CPSCourse-TUM-HN/connecTUM/kicad_schematics/Adafruit PCA9685 rev C.kicad_sch

## KiCad design kicad_schematics/Adafruit PCA9685 rev C.kicad_sch (2025-07-12)

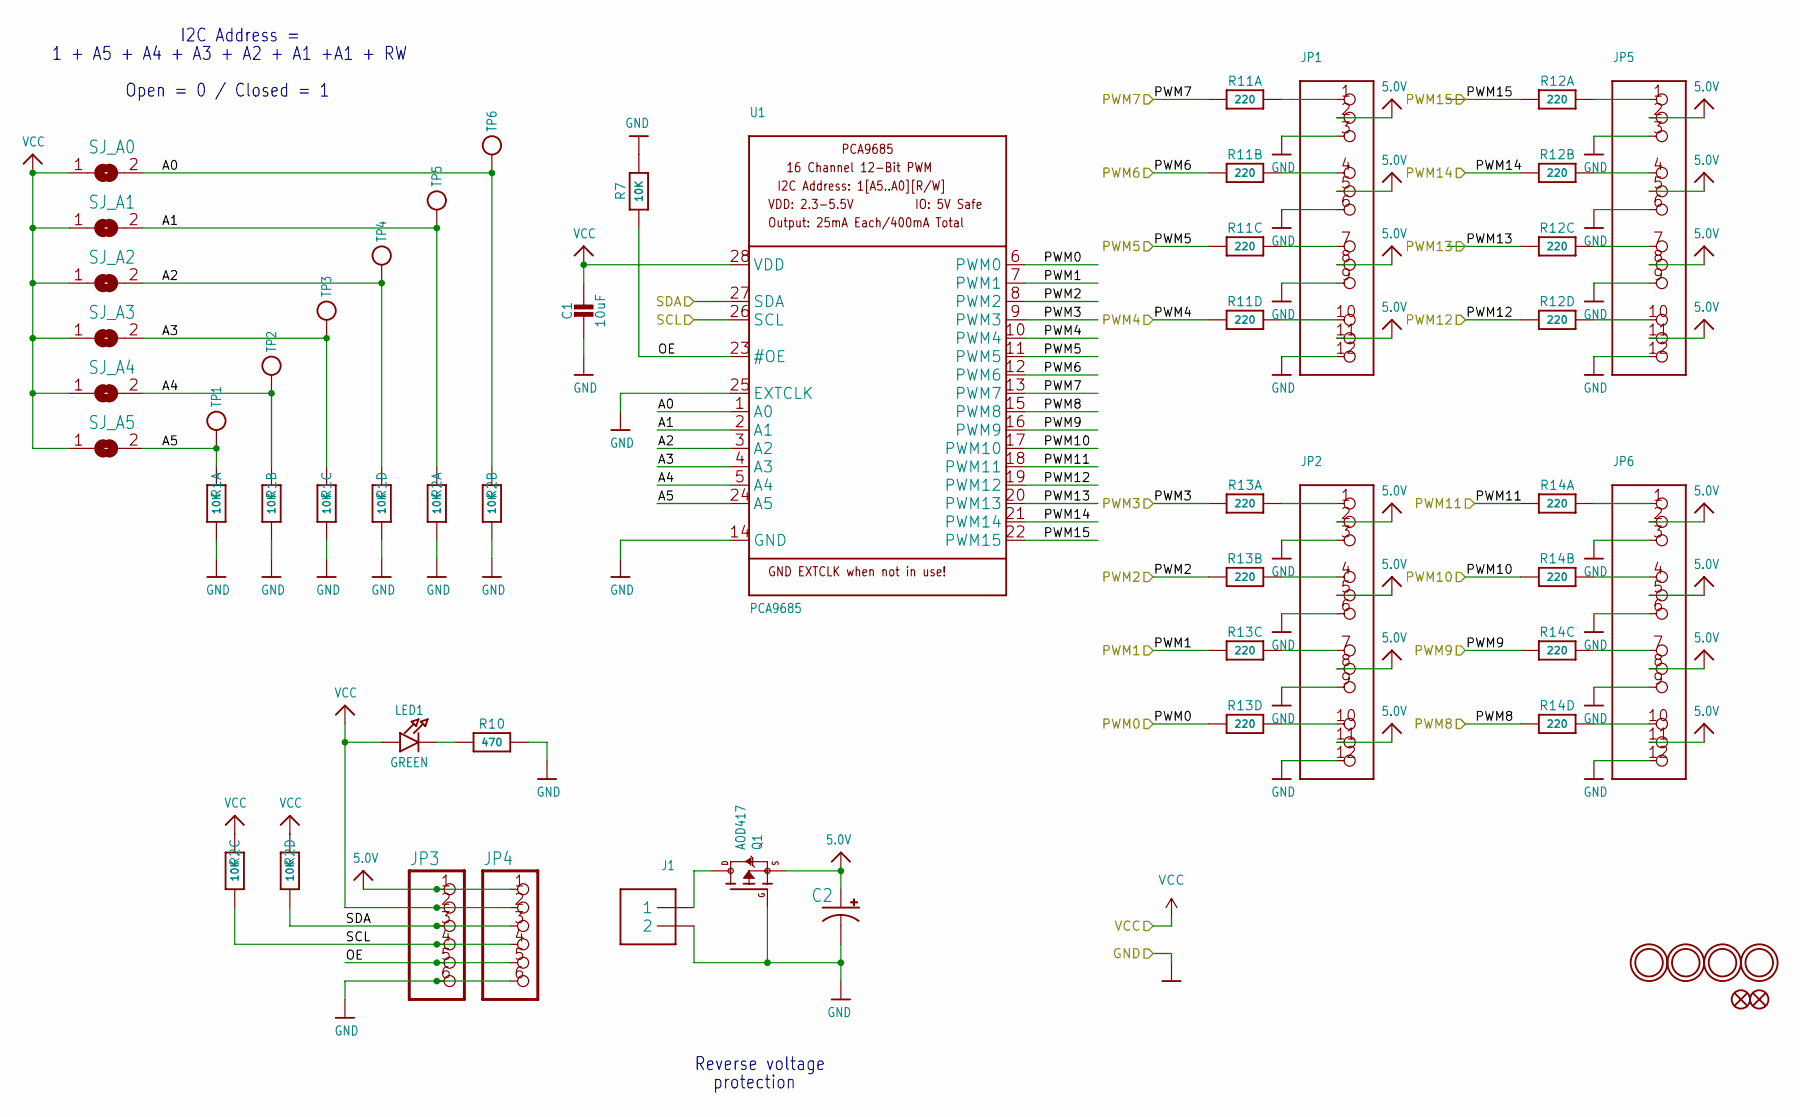
[picture p21: schematic Adafruit PCA9685 rev C.kicad_sch]

Parts:
01: (no value)
C1: 10uF; 0805-NO
C2: CPOL-USE3.5-8; E3,5-8
FID1, FID2: FIDUCIAL""; FIDUCIAL_1MM
J1: TERMBLOCK_1X2; TERMBLOCK_1X2-3.5MM
JP1, JP2, JP5, JP6: HEADER-3X04; 3X04
JP3, JP4: PINHD-1X6CB; 1X06-CLEANBIG
LED1: GREEN; CHIPLED_0805_NOOUTLINE
Q1: AOD417; TO252
R1, R2: 10K; RESPACK_4X0603
R7: 10K; 0805-NO
R10: 470; _0805MP
R11, R12, R13, R14: 220; RESPACK_4X0603
SJ_A0, SJ_A1, SJ_A2, SJ_A3, SJ_A4, SJ_A5: SOLDERJUMPERREFLOW_NOPASTE; SOLDERJUMPER_REFLOW_NOPASTE
TP1, TP2, TP3, TP4, TP5, TP6: TESTPOINTROUND1MM; TESTPOINT_ROUND_1MM
U1: PCA9685; TSSOP28
U$47, U$48, U$49, U$50: MOUNTINGHOLE2.5; MOUNTINGHOLE_2.5_PLATED

Connections:
5.0V: C2.+, JP1.2, JP1.5, JP1.8, JP1.11, JP2.2, JP2.5, JP2.8, JP2.11, JP3.1, JP4.1, JP5.2, JP5.5, JP5.8, JP5.11, JP6.2, JP6.5, JP6.8, JP6.11, Q1.2 (S)
A0: R2.7 (2), SJ_A0.2, TP6.P$1, U1.1 (A0)
A1: R2.8 (2), SJ_A1.2, TP5.P$1, U1.2 (A1)
A2: R1.5 (2), SJ_A2.2, TP4.P$1, U1.3 (A2)
A3: R1.6 (2), SJ_A3.2, TP3.P$1, U1.4 (A3)
A4: R1.7 (2), SJ_A4.2, TP2.P$1, U1.5 (A4)
A5: R1.8 (2), SJ_A5.2, TP1.P$1, U1.24 (A5)
GND: 01.1, C1.2, C2.-, J1.2, JP1.3, JP1.6, JP1.9, JP1.12, JP2.3, JP2.6, JP2.9, JP2.12, JP3.6, JP4.6, JP5.3, JP5.6, JP5.9, JP5.12, JP6.3, JP6.6, JP6.9, JP6.12, Q1.1 (G), R1.1, R1.2 (1), R1.3 (1), R1.4 (1), R2.1, R2.2 (1), R7.2, R10.2, U1.14 (GND), U1.25 (EXTCLK)
unnamed: J1.1, Q1.3 (D)
unnamed: JP1.1, R11.8 (2)
unnamed: JP1.4, R11.7 (2)
unnamed: JP1.7, R11.6 (2)
unnamed: JP1.10, R11.5 (2)
unnamed: JP2.1, R13.8 (2)
unnamed: JP2.4, R13.7 (2)
unnamed: JP2.7, R13.6 (2)
unnamed: JP2.10, R13.5 (2)
unnamed: JP5.1, R12.8 (2)
unnamed: JP5.4, R12.7 (2)
unnamed: JP5.7, R12.6 (2)
unnamed: JP5.10, R12.5 (2)
unnamed: JP6.1, R14.8 (2)
unnamed: JP6.4, R14.7 (2)
unnamed: JP6.7, R14.6 (2)
unnamed: JP6.10, R14.5 (2)
unnamed: LED1.C, R10.1
OE: JP3.5, JP4.5, R7.1, U1.23 (#OE)
PWM0: R13.4 (1), U1.6 (PWM0)
PWM1: R13.3 (1), U1.7 (PWM1)
PWM2: R13.2 (1), U1.8 (PWM2)
PWM3: R13.1, U1.9 (PWM3)
PWM4: R11.4 (1), U1.10 (PWM4)
PWM5: R11.3 (1), U1.11 (PWM5)
PWM6: R11.2 (1), U1.12 (PWM6)
PWM7: R11.1, U1.13 (PWM7)
PWM8: R14.4 (1), U1.15 (PWM8)
PWM9: R14.3 (1), U1.16 (PWM9)
PWM10: R14.2 (1), U1.17 (PWM10)
PWM11: R14.1, U1.18 (PWM11)
PWM12: R12.4 (1), U1.19 (PWM12)
PWM13: R12.3 (1), U1.20 (PWM13)
PWM14: R12.2 (1), U1.21 (PWM14)
PWM15: R12.1, U1.22 (PWM15)
SCL: JP3.4, JP4.4, R2.3 (1), U1.26 (SCL)
SDA: JP3.3, JP4.3, R2.4 (1), U1.27 (SDA)
VCC: C1.1, JP3.2, JP4.2, LED1.A, R2.5 (2), R2.6 (2), SJ_A0.1, SJ_A1.1, SJ_A2.1, SJ_A3.1, SJ_A4.1, SJ_A5.1, U1.28 (VDD)

Notes on the sheet:
1 + A5 + A4 + A3 + A2 + A1 +A1 + RW
Open = 0 / Closed = 1
Reverse voltage
I2C Address =
protection
