CPSCourse-TUM-HN/connecTUM/kicad_schematics/Adafruit TMC2209 Stepper Motor Driver.kicad_sch

## KiCad design kicad_schematics/Adafruit TMC2209 Stepper Motor Driver.kicad_sch (2025-07-12)

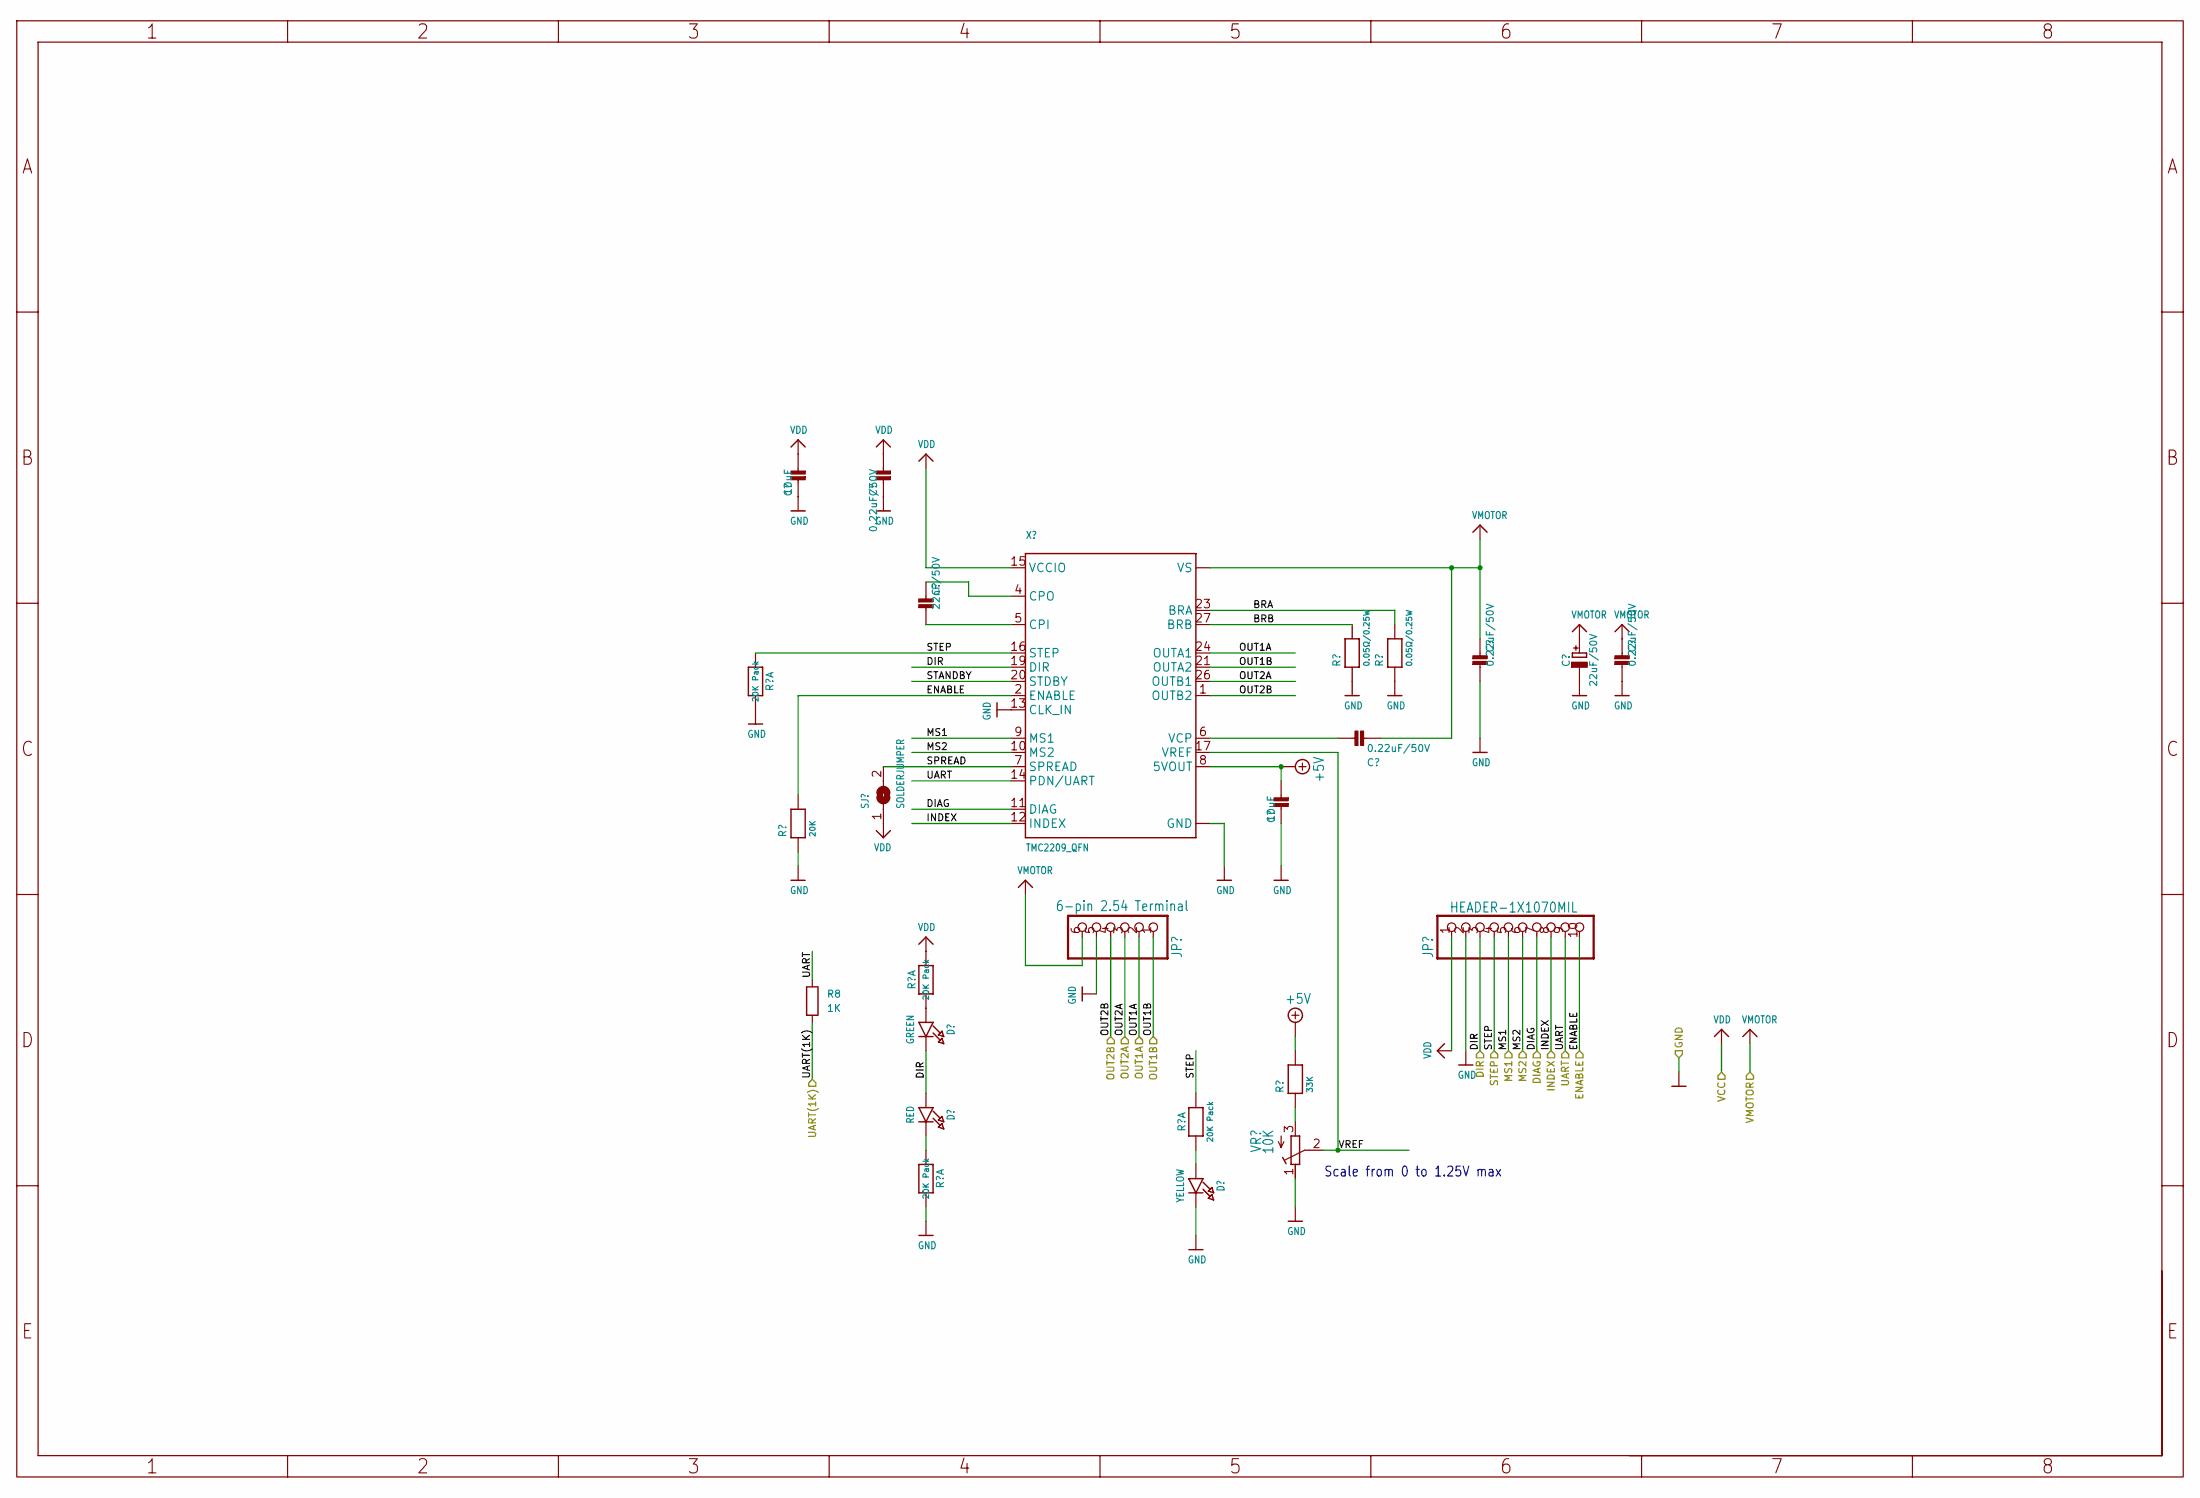
[picture p22: schematic Adafruit TMC2209 Stepper Motor Driver.kicad_sch]

Parts:
01: (no value)
C1: 22nF/50V; 0603-NO
C2, C6: 10uF; 0805-NO
C3, C5, C7, C8: 0.22uF/50V; 0603-NO
C4: 22uF/50V; PANASONIC_C
D1: RED; CHIPLED_0603_NOOUTLINE
D2: YELLOW; CHIPLED_0603_NOOUTLINE
D3: GREEN; CHIPLED_0603_NOOUTLINE
JP1: 6-pin 2.54 Terminal; 1X06_2.54MMTERMINAL
JP4: HEADER-1X1070MIL; 1X10_ROUND70
R1, R2: 0.05Ω/0.25W; 0603-NO
R3: 20K; 0603-NO
R4: 33K; 0603-NO
R5: 20K Pack; RESPACK_4X0603
R8: 1K
SJ1: SOLDERJUMPER; SOLDERJUMPER_ARROW_NOPASTE
VR1: 10K; RTRIM3314J
X1: TMC2209_QFN; QFN28_5MM_MICROCHIP

Connections:
+5V: C6.2, R4.2, X1.8 (5VOUT)
BRA: R2.2, X1.23 (BRA)
BRB: R1.2, X1.27 (BRB)
DIAG: JP4.7, X1.11 (DIAG)
DIR: D1.A, D3.C, JP4.3, X1.19 (DIR)
ENABLE: JP4.10, R3.2, X1.2 (ENABLE)
GND: 01.1, C2.1, C3.1, C4.-, C5.2, C6.1, C8.2, D2.C, JP1.5, JP4.2, R1.1, R2.1, R3.1, R5.8 (2), VR1.1 (E), X1.3 (GND), X1.13 (CLK_IN), X1.18 (GND), X1.25 (GND), X1.THERMAL (GND)
INDEX: JP4.8, X1.12 (INDEX)
MS1: JP4.5, X1.9 (MS1)
MS2: JP4.6, X1.10 (MS2)
unnamed: C1.1, X1.4 (CPO)
unnamed: C1.2, X1.5 (CPI)
unnamed: C7.1, X1.6 (VCP)
unnamed: D1.C, R5.1
unnamed: D2.A, R5.1
unnamed: D3.A, R5.1
unnamed: R4.1, VR1.3 (A)
OUT1A: JP1.2, X1.24 (OUTA1)
OUT1B: JP1.1, X1.21 (OUTA2)
OUT2A: JP1.3, X1.26 (OUTB1)
OUT2B: JP1.4, X1.1 (OUTB2)
SPREAD: SJ1.2, X1.7 (SPREAD)
STANDBY: X1.20 (STDBY)
STEP: JP4.4, R5.1, R5.8 (2), X1.16 (STEP)
UART: JP4.9, R8.1, X1.14 (PDN/UART)
UART(1K): R8.2
VDD: C2.2, C3.2, JP4.1, R5.8 (2), SJ1.1, X1.15 (VCCIO)
VMOTOR: C4.+, C5.1, C7.2, C8.1, JP1.6, X1.22 (VS), X1.28 (VS)
VREF: VR1.2 (S), X1.17 (VREF)

Notes on the sheet:
Scale from 0 to 1.25V max
