CPSCourse-TUM-HN/connecTUM/kicad_schematics/connecTUM.kicad_sch

## KiCad design kicad_schematics/connecTUM.kicad_sch (2025-07-12)

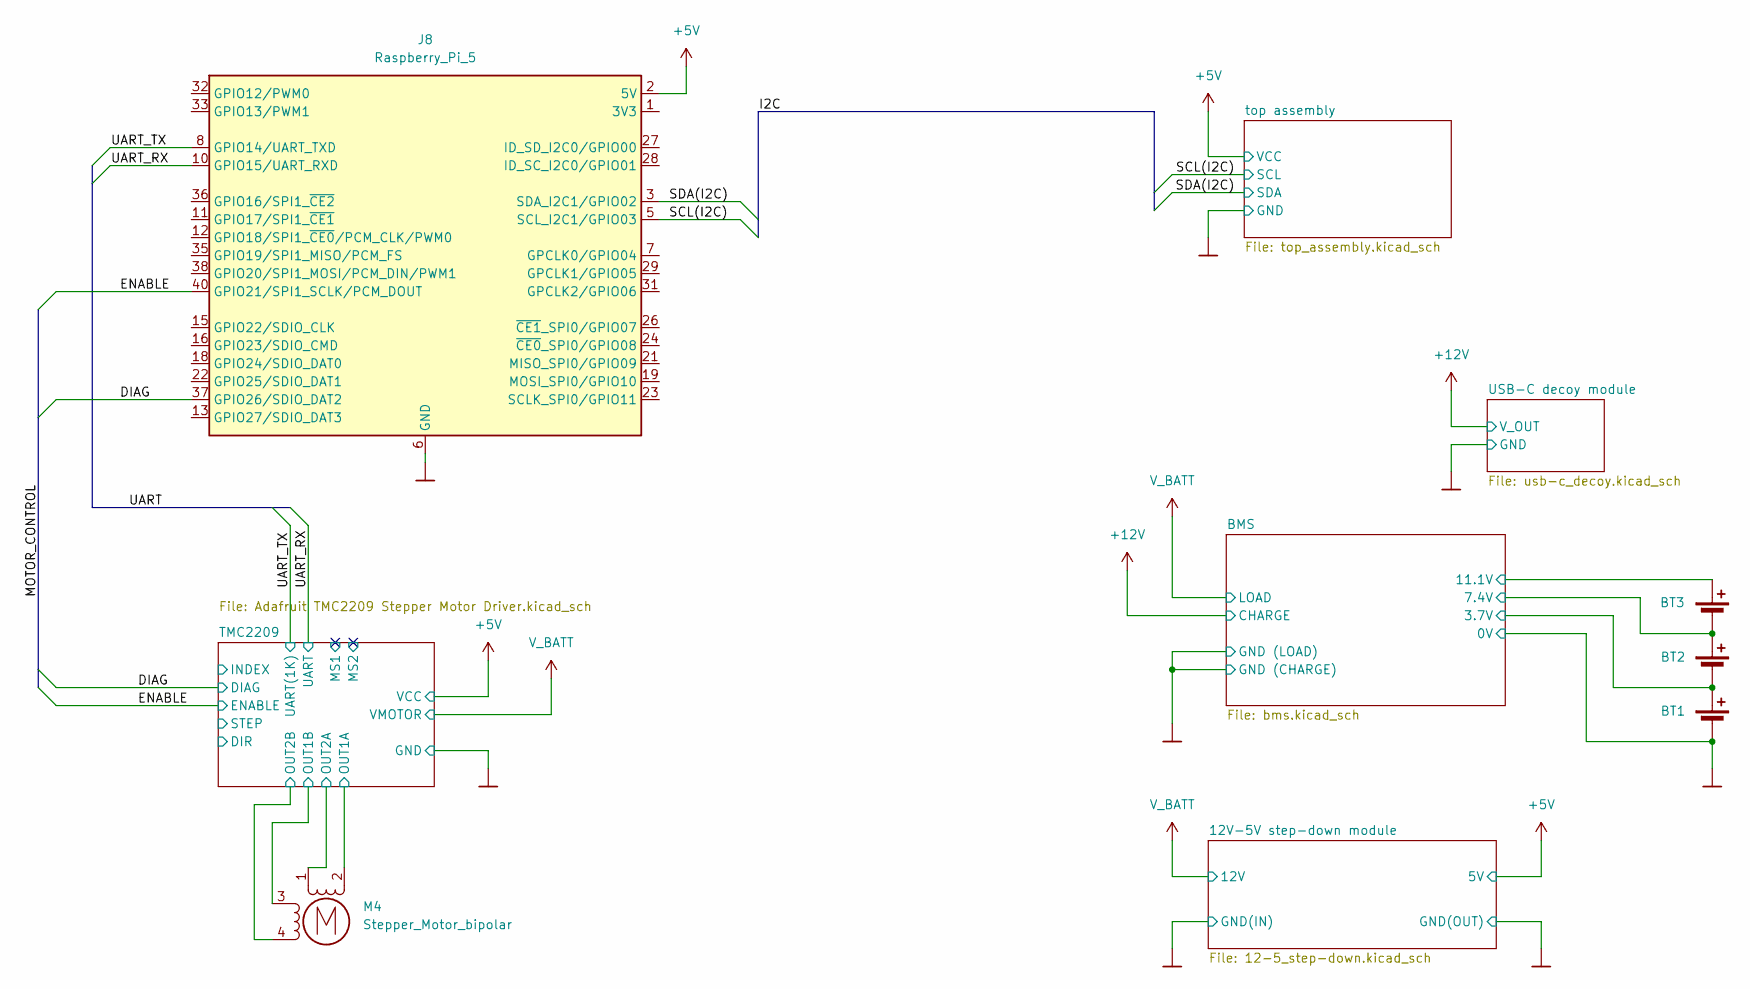
[picture p23: schematic connecTUM.kicad_sch]

Parts:
01, 0101: (no value)
BT1, BT2, BT3: Battery_Cell
J8: Raspberry_Pi_5
M4: Stepper_Motor_bipolar

Connections:
0V: 01.1, BT1.2 (-)
3.7V: BT1.1 (+), BT2.2 (-)
7.4V: BT2.1 (+), BT3.2 (-)
11.1V: BT3.1 (+)
+5V: J8.2 (5V), J8.4 (5V)
DIAG: J8.37 (GPIO26/SDIO_DAT2)
ENABLE: J8.40 (GPIO21/SPI1_SCLK/PCM_DOUT)
GND: 01.1
GND (CHARGE): 0101.1
GND(IN): 01.1
GND(OUT): 01.1
unnamed: 01.1, J8.6 (GND), J8.9 (GND), J8.14 (GND), J8.20 (GND), J8.25 (GND), J8.30 (GND), J8.34 (GND), J8.39 (GND)
unnamed: J8.1 (3V3), J8.17 (3V3)
OUT1A: M4.2 (-)
OUT1B: M4.3
OUT2A: M4.1
OUT2B: M4.4
SCL(I2C): J8.5 (SCL_I2C1/GPIO03)
SDA(I2C): J8.3 (SDA_I2C1/GPIO02)
UART_RX: J8.10 (GPIO15/UART_RXD)
UART_TX: J8.8 (GPIO14/UART_TXD)
