CPSCourse-TUM-HN/connecTUM/kicad_schematics/pcf8574.kicad_sch

## KiCad design kicad_schematics/pcf8574.kicad_sch (2025-07-12)

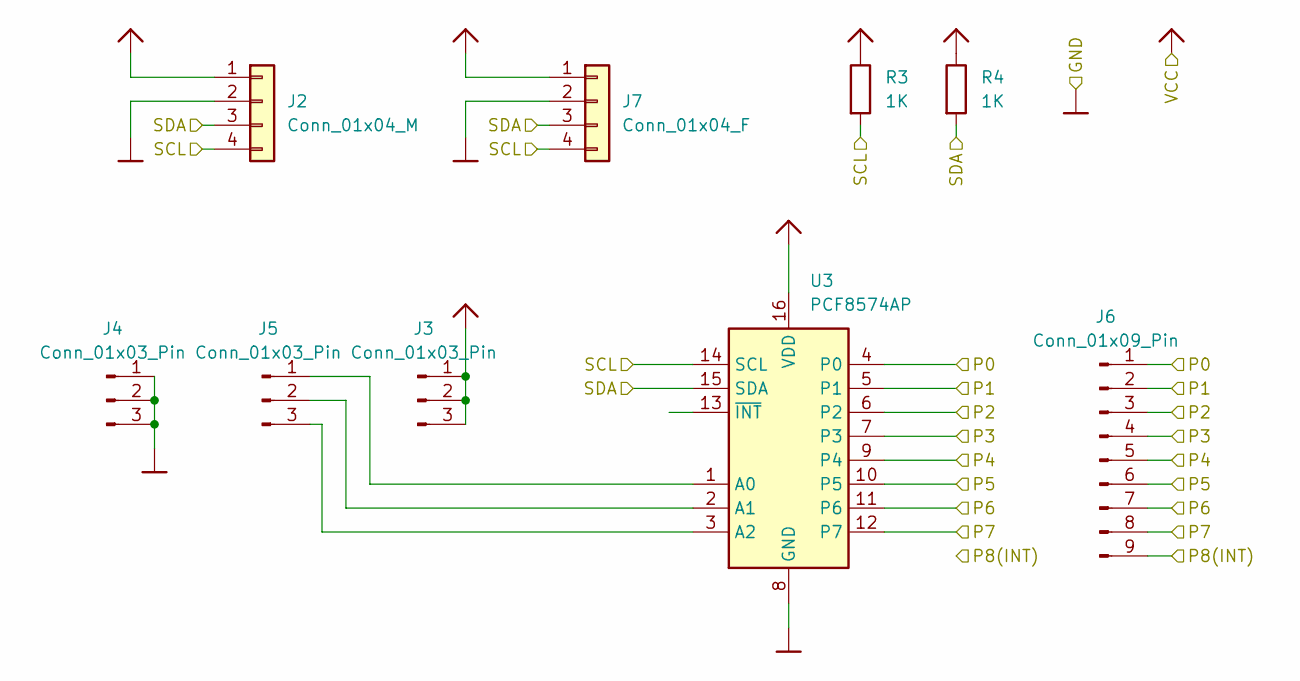
[picture p24: schematic pcf8574.kicad_sch]

Parts:
01, 0101: (no value)
J2: Conn_01x04_M; PinHeader_1x04_P2.00mm_Horizontal
J3, J4, J5: Conn_01x03_Pin; PinHeader_1x03_P2.00mm_Vertical
J6: Conn_01x09_Pin; PinHeader_1x09_P2.00mm_Vertical
J7: Conn_01x04_F; PinSocket_1x04_P2.00mm_Horizontal
R3, R4: 1K
U3: PCF8574AP; DIP-16_W7.62mm

Connections:
GND: 01.1
unnamed: 01.1, J2.2, J4.1, J4.2, J4.3, U3.8 (GND)
unnamed: 0101.1, J7.2
unnamed: J5.1, U3.1 (A0)
unnamed: J5.2, U3.2 (A1)
unnamed: J5.3, U3.3 (A2)
P0: J6.1, U3.4 (P0)
P1: J6.2, U3.5 (P1)
P2: J6.3, U3.6 (P2)
P3: J6.4, U3.7 (P3)
P4: J6.5, U3.9 (P4)
P5: J6.6, U3.10 (P5)
P6: J6.7, U3.11 (P6)
P7: J6.8, U3.12 (P7)
P8(INT): J6.9
SCL: J2.4, J7.4, R3.2, U3.14 (SCL)
SDA: J2.3, J7.3, R4.2, U3.15 (SDA)
~: J2.1, J3.1, J3.2, J3.3, J7.1, R3.1, R4.1, U3.16 (VDD)
