CPSCourse-TUM-HN/connecTUM/kicad_schematics/top_assembly.kicad_sch

## KiCad design kicad_schematics/top_assembly.kicad_sch (2025-07-12)

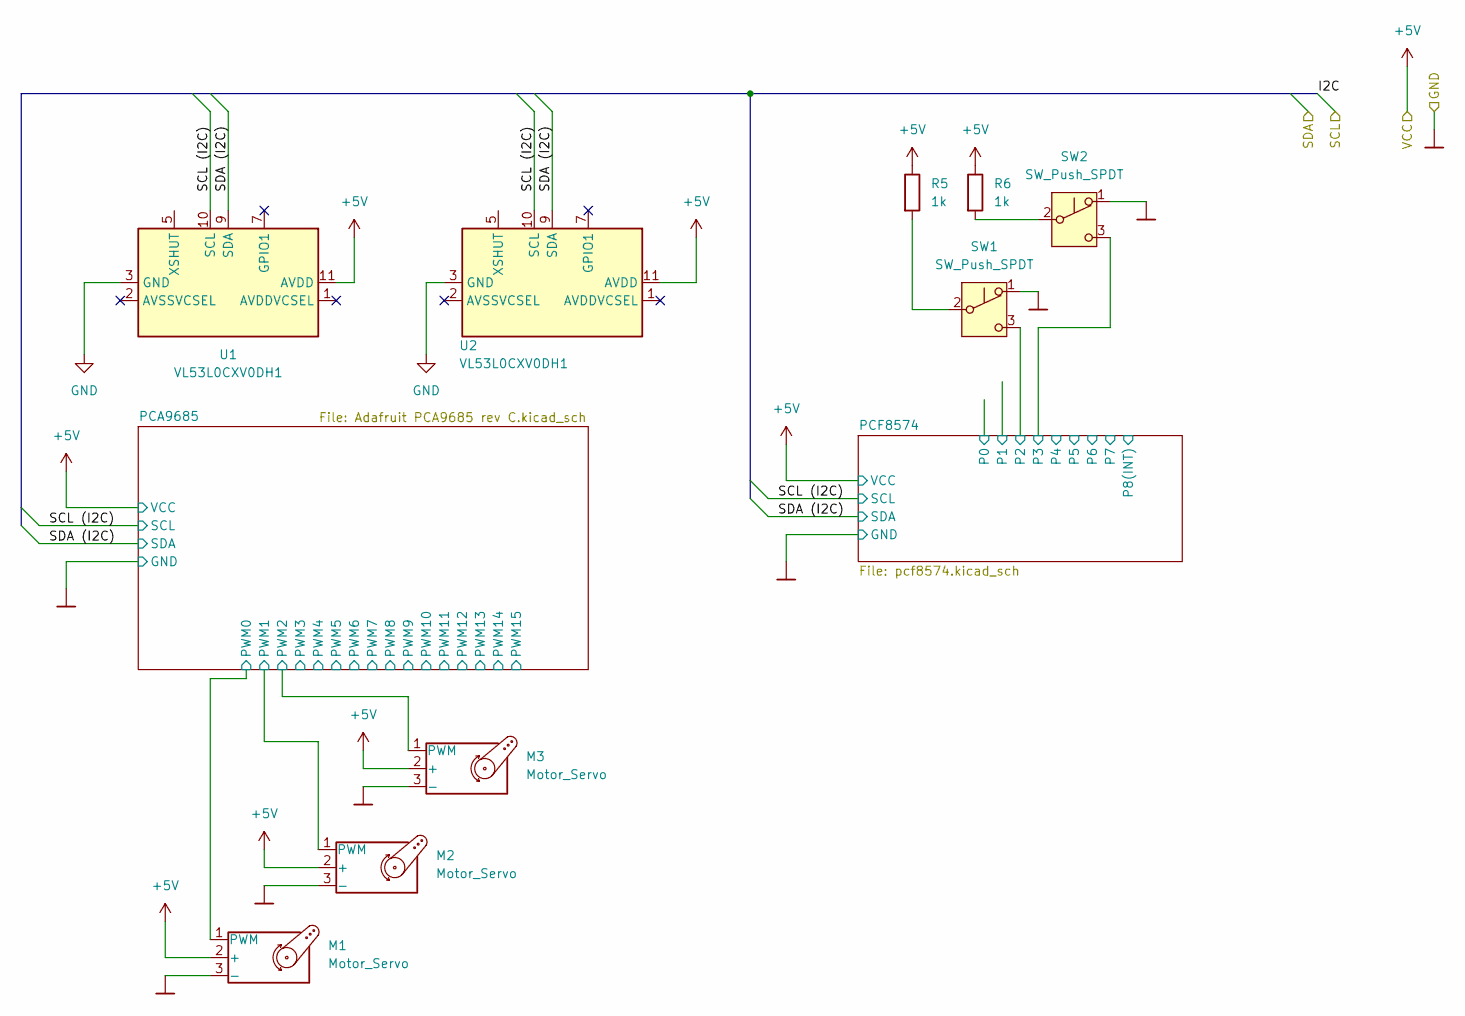
[picture p25: schematic top_assembly.kicad_sch]

Parts:
01: (no value)
M1, M2, M3: Motor_Servo
R5, R6: 1k
SW1, SW2: SW_Push_SPDT
U1, U2: VL53L0CXV0DH1; ST_VL53L1x

Connections:
+5V: M1.2 (+), M2.2 (+), M3.2 (+), R5.1, R6.1, U1.11 (AVDD), U2.11 (AVDD)
GND: 01.1, U1.3 (GND), U1.4 (GND), U1.6 (GND), U1.12 (GND), U2.3 (GND), U2.4 (GND), U2.6 (GND), U2.12 (GND)
unnamed: 01.1, M1.3 (-), M2.3 (-), M3.3 (-), SW1.1 (A), SW2.1 (A)
unnamed: R5.2, SW1.2 (B)
unnamed: R6.2, SW2.2 (B)
P2: SW1.3 (C)
P3: SW2.3 (C)
PWM0: M1.1 (PWM)
PWM1: M2.1 (PWM)
PWM2: M3.1 (PWM)
SCL (I2C): U1.10 (SCL), U2.10 (SCL)
SDA (I2C): U1.9 (SDA), U2.9 (SDA)
