CPSCourse-TUM-HN/connecTUM/arduino sketch/srceen_ui.ino

/*
    Autoscroll.ino
    2013 Copyright (c) Seeed Technology Inc.  All right reserved.

    Author:Loovee
    2013-9-18

    Grove - Serial LCD RGB Backlight demo.

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
    You should have received a copy of the GNU Lesser General Public
    License along with this library; if not, write to the Free Software
    Foundation, Inc., 51 Franklin St, Fifth Floor, Boston, MA  02110-1301  USA
*/

#include <Wire.h>
#include "rgb_lcd.h"

rgb_lcd lcd;
int pot = A0;
int value = 0;
int new_value = 0;

void setup() {
    // Serial.begin(9600);
    // set up the LCD's number of columns and rows:
    lcd.begin(16, 2);
}

void loop() {
    // set the cursor to (0,0):
    new_value = analogRead(pot);

    if (abs(new_value - value) >= 3) {
        lcd.setCursor(new_value / 68, 0);
        // Serial.print(new_value % 16);
        // Serial.print("\n");
    }
    else {
        lcd.setCursor(value, 0);
    }

    lcd.print('X');
    
    delay(500);
    lcd.clear();
}

/*********************************************************************************************************
    END FILE
*********************************************************************************************************/
